BogdanCiocea/OpenBook/Images/baterie.png

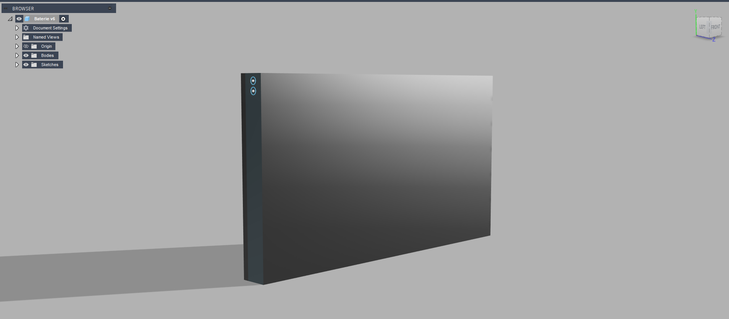
Images/baterie.png
