BogdanCiocea/OpenBook/Images/ecran2.png

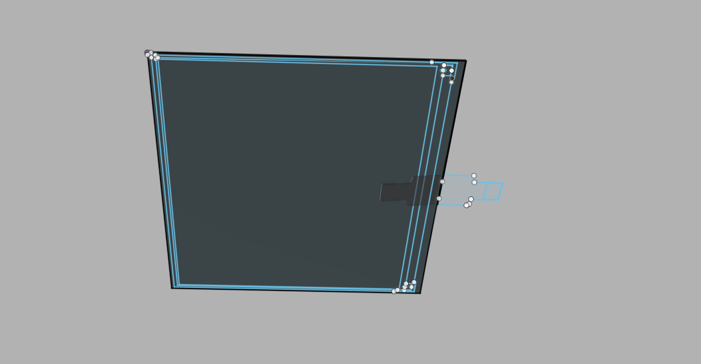
Images/ecran2.png
