BogdanCiocea/OpenBook/Images/placuta1.png

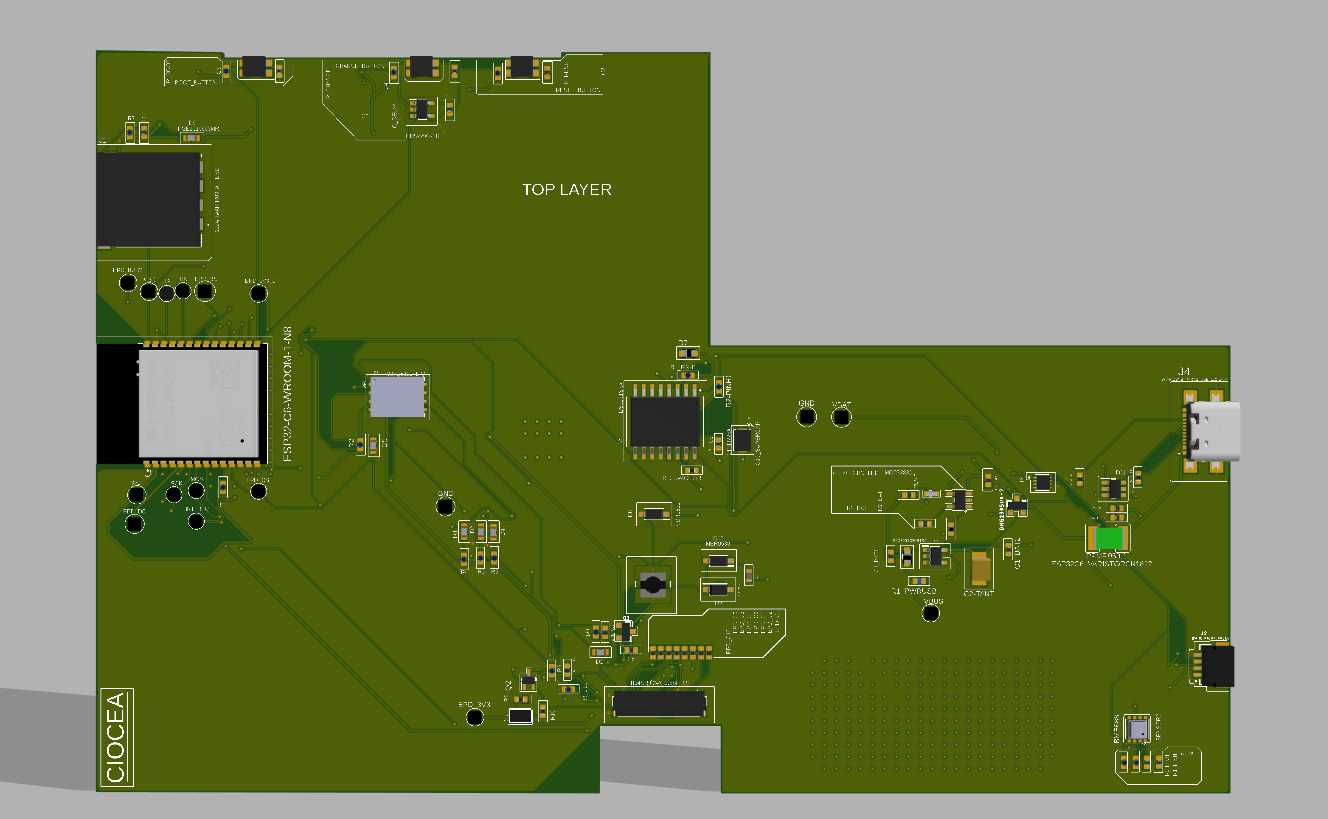
Images/placuta1.png
