BogdanCiocea/OpenBook/Images/placuta3.png

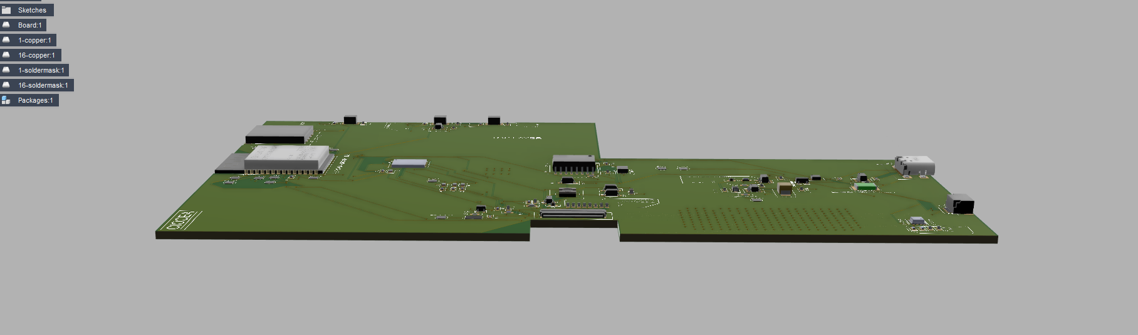
Images/placuta3.png
